thebiguno/stubby/processing/src/ca/digitalcave/stubby/Protocol.java

package ca.digitalcave.stubby;

import java.util.Collections;
import java.util.LinkedList;
import java.util.List;
import java.util.concurrent.ConcurrentHashMap;
import java.util.logging.Logger;

import processing.serial.Serial;


public class Protocol {
	private final Serial serial;

	private long lastControllerIdMessageSent = 0;

	private final ConcurrentHashMap<Integer, List<Message>> mailbox = new ConcurrentHashMap<Integer, List<Message>>();

	public final int START = 0x7e;
	public final int ESCAPE = 0x7d;

	private final int MAX_SIZE = 255;
	
	public static final int ANNOUNCE_CONTROL_ID = 0x00;
	
	public static final int SEND_ACKNOWLEDGE = 0x01;
	public static final int SEND_COMPLETE = 0x02;
	
	public static final int REQUEST_ENABLE_DEBUG = 0x03;
	public static final int REQUEST_DISABLE_DEBUG = 0x04;
	public static final int SEND_DEBUG = 0x05;

	public static final int REQUEST_POWER_ON	= 0x20;
	public static final int REQUEST_POWER_OFF = 0x21;

	public static final int REQUEST_MOVE = 0x22;
	public static final int REQUEST_TURN = 0x23;
	public static final int REQUEST_TRANSLATE = 0x24;
	public static final int REQUEST_ROTATE = 0x25;

	public static final int REQUEST_HEADING = 0x26;
	public static final int SEND_HEADING = 0x27;

	public static final int REQUEST_DISTANCE = 0x28;
	public static final int SEND_DISTANCE = 0x29;

	public static final int REQUEST_OPTICAL = 0x2A;
	public static final int SEND_OPTICAL = 0x2B;

	public static final int REQUEST_SET_LED = 0x2C;

	boolean isMessageWaiting(int command){
		return (mailbox.get(command) != null && mailbox.get(command).size() > 0);
	}
	Message popMessage(int command){
		if (mailbox.get(command) == null || mailbox.get(command).size() == 0) return null;
		return mailbox.get(command).remove(0);
	}
	boolean waitForAcknowledge(int command){
		while (!isMessageWaiting(Protocol.SEND_ACKNOWLEDGE)){
			try {Thread.sleep(10);} catch (InterruptedException e){} 
		}
		return (popMessage(Protocol.SEND_ACKNOWLEDGE).getCommand() == command);
	}
	boolean waitForComplete(int command){
		while (!isMessageWaiting(Protocol.SEND_COMPLETE)){
			try {Thread.sleep(10);} catch (InterruptedException e){} 
		}
		return (popMessage(Protocol.SEND_COMPLETE).getCommand() == command);
	}
	
	public Protocol(Serial serial) {
		this.serial = serial;
	}
	
	public Serial getSerial() {
		return serial;
	}
	
	protected void dispatch(int cmd, int[] data, int length){
		if (cmd == SEND_DEBUG){
			StringBuilder sb = new StringBuilder();
			for (int i = 0; i < length; i++){
				if (data[i] == 0) break;
				sb.append((char) data[i]);
			}
			System.out.println("Debug: " + sb.toString());
		}
		else {
			StringBuilder sb = new StringBuilder();
			for (int i = 0; i < length; i++){
				sb.append(Integer.toHexString(data[i])).append(" ");
			}
			Logger.getLogger(this.getClass().getName()).info("Received command: " + Integer.toHexString(cmd) + ", value: [ " + sb.toString() + "]");
			if (mailbox.get(cmd) == null) mailbox.put(cmd, Collections.synchronizedList(new LinkedList<Message>()));
			mailbox.get(cmd).add(new Message(cmd, data));
			if (mailbox.get(cmd).size() > 255){
				mailbox.get(cmd).remove(0);	//Limit the length of the array by removing the oldest entries.
			}
		}
	}

	private int[] buf = new int[MAX_SIZE];
	private boolean err = false;
	private boolean esc = false;
	private int pos = 0;
	private int len = 0;
	private int cmd = 0;
	private int chk = 0x00;
	
	public void receiveByte(int b) {
		if (err && b == START) {
			// recover from error condition
			System.err.println("Recover from error condition");
			err = false;
			pos = 0;
		} else if (err) {
			return;
		}

		if (pos > 0 && b == START) {
			// unexpected start of frame
			System.err.println("Unexpected start of frame");
			err = true;
			return;
		}

		if (pos > 0 && b == ESCAPE) {
			// unescape next byte
			esc = true;
			return;
		}

		if (esc) {
			// unescape current byte
			b = 0x20 ^ b;
			esc = false;
		}

		if (pos > 1) {
			chk = (chk + b) & 0xFF;
		}

		switch (pos) {
		case 0:
			pos++;
			return;
		case 1:
			len = b;
			pos++;
			return;
		case 2:
			cmd = b;
			pos++;
			return;
		default:
			if (pos > MAX_SIZE) {
				// this probably can't happen
				System.err.println("Position > MAX_SIZE");
				return;
			}
			if (pos == (len + 2)) {
				if (chk == 0xff) {
					dispatch(cmd, buf, pos - 3);
				} else {
					err = true;
					System.err.println("Invalid checksum");
				}
				pos = 0;
				chk = 0;
			} else {
				buf[pos++ - 3] = b;
			}
		}
	}

	private void sendByte(int b, boolean escape) {
		if (escape && (b == START || b == ESCAPE)) {
			serial.write(ESCAPE);
			serial.write(b ^ 0x20);
		} else {
			serial.write(b);
		}
	}

	public boolean sendMessageAndBlockForAck(Message message, long ackTimeout, int retryCount) {
		for (int retry = 0; retry < retryCount; retry++){
			sendMessage(message);
			for (long i = 0; i < ackTimeout; i++){
				try {Thread.sleep(1);} catch (InterruptedException e){}
				if (isMessageWaiting(Protocol.SEND_ACKNOWLEDGE)){
					final Message ackMessage = popMessage(Protocol.SEND_ACKNOWLEDGE);
					if (ackMessage.getData()[0] == message.getCommand()){
						return true;
					}
					else {
						Logger.getLogger(this.getClass().getName()).warning("Ack command (" + Integer.toHexString(ackMessage.getData()[0]) + ") did not match expected command (" + Integer.toHexString(message.getCommand()) + ")");
					}
				}
			}
			Logger.getLogger(this.getClass().getName()).warning("Attempt to send command (" + Integer.toHexString(message.getCommand()) + ") timed out.");
		}
		
		Logger.getLogger(this.getClass().getName()).warning("Attempt to re-send command (" + Integer.toHexString(message.getCommand()) + ") failed.");
		return false;
	}
	
	public Message sendMessageAndBlockForReply(Message message, int replyMessageType, long ackTimeout, int retryCount) {
		for (int retry = 0; retry < retryCount; retry++){
			sendMessage(message);
			for (long i = 0; i < ackTimeout; i++){
				try {Thread.sleep(1);} catch (InterruptedException e){}
				if (isMessageWaiting(replyMessageType)){
					final Message responseMessage = popMessage(replyMessageType);
					return responseMessage;
				}
			}
			Logger.getLogger(this.getClass().getName()).warning("Attempt to send command (" + Integer.toHexString(message.getCommand()) + ") timed out.");
		}
		
		Logger.getLogger(this.getClass().getName()).warning("Attempt to re-send command (" + Integer.toHexString(message.getCommand()) + ") failed.");
		return null;
	}
	
	public boolean sendMessage(Message message) {
		if (lastControllerIdMessageSent + 3000 < System.currentTimeMillis()){
			//If we have not sent the control ID message in the previous three seconds, do so now.
			sendByte(START, false);
			sendByte(2, true);
			sendByte(ANNOUNCE_CONTROL_ID, true);
			sendByte('P', true);	//Data
			sendByte(0xFF - 'P', true);	//Checksum 
			lastControllerIdMessageSent = System.currentTimeMillis();
		}
		
		sendByte(START, false);
		sendByte(message.getData().length + 1, true);
		sendByte(message.getCommand(), true);

		int checksum = message.getCommand() & 0xFF;

		for (int i = 0; i < message.getData().length; i++) {
			sendByte(message.getData()[i], true);
			checksum += message.getData()[i];
			checksum &= 0xFF;
		}

		checksum = (0xFF - checksum);

		sendByte(checksum, true);
		
		StringBuilder sb = new StringBuilder();
		for (int i = 0; i < message.getData().length; i++){
			sb.append(Integer.toHexString(message.getData()[i])).append(" ");
		}
		Logger.getLogger(this.getClass().getName()).info("Sent command: " + Integer.toHexString(message.getCommand()) + ", value: [ " + sb.toString() + "]");
		
		return true;
	}

	public static double byteToRadian(int x) {
		float r = 0.024639942381096f * x;
		return (r > Math.PI) ? r - (2.0 * Math.PI) : r; // convert quadrants III & IV into negative values
	}
	public static int radianToByte(double x) {
		double r = x < 0 ? 2.0 * Math.PI + x : x; // convert quadrants III & IV into positive values
		return (int) (40.584510488433314f * r);
	}

	public static void floatToArr(double f, int[] b, int offset) {
		int bits = Float.floatToIntBits((float) f);
		for (int i = offset; i < offset + 4; i++) {
			b[i] = bits & 0xFF;
			bits = bits >> 8;
		}		
	}
	public static double arrToFloat(int[] b, int offset) {
		int bits = 0;
		for (int i = offset + 3; i >= offset; i--){
			bits = (bits << 8) + b[i];
		}
		return Float.intBitsToFloat(bits);
	}
}
